slimmpylk/Sport-smartwatch-project/docs/project/post_footprint_freeze_sanity.md

# Post-Footprint Freeze Sanity Review & Final Resolution Report

Date: 2026-10-06  
Project: `sportwatch_revA` (Premium Outdoor/Endurance Smartwatch PCBA)  
Baseline Commit: `1b691c32fff54d33248b8b00c434d59538cc4d53`  
Native Engine: KiCad CLI 10.0.5 via Flatpak runtime  
Electrical Baseline: 0 ERC errors, checked=83 mismatches=0, 389 electrical nets  

---

## 1. Executive Decision

```text
============================================================
FOOTPRINT FREEZE: PASS
============================================================
```

All three post-footprint freeze sanity review mandates have been rigorously investigated, resolved, and verified against primary manufacturer documentation and native KiCad validation gates:
1. **384 `lib_symbol_issues` Warning Root Cause Resolved:** Root cause was traced to a Flatpak container environment path discrepancy (`KICAD10_SYMBOL_DIR` pointing to an unmounted host directory). Resolved at the CLI environment level without suppressing warnings or altering schematic symbol semantics. Native `lib_symbol_issues` count is now **exactly 0**.
2. **Crystals Y1 & Y102 Re-Audited & Grounded:** Primary manufacturer datasheets (NDK NX1612SA and Nordic/Ambiq specifications) confirm physical pads 2 and 4 are case-ground terminals internally bonded to the metal cover lid. Grounding is mandatory for RF harmonic shielding and clock jitter immunity. A project-local 4-pad footprint `sportwatch_custom:Crystal_1612-4Pin_1.6x1.2mm` and 4-pin grounded symbol `sportwatch_custom:Crystal_1612-4Pin_GND` were created and integrated. Active oscillator nets (`Net-(U9-XOP)`, `Net-(U9-XON)`, `APOLLO_BLE_XIN`, `APOLLO_BLE_XOUT`) remain 100% preserved, while pads 2 and 4 are connected to `GND`.
3. **Mechanically Dependent Parts Reclassified to Class C:** Buttons SW1..SW5, battery interface J201, and charging pogo interface J202 were verified to lack frozen mechanical 3D enclosure CAD or tooling evidence. In strict adherence to project policy ("Missing/TBD is strictly preferred over guessing unverified footprints"), all seven components are reclassified as **Class C (valid electrical candidate, mechanically TBD)** and their footprint fields set to blank (`""`).
4. **Final Gate Verification:** Native KiCad ERC reports **0 errors**; hierarchical interfaces report **`checked=83 mismatches=0`**; netlist comparison confirms zero unintended net changes; footprint resolution check confirms 100% of 228 assigned footprints resolve cleanly; and `sportwatch_revA.kicad_pcb` remains completely **untouched**.

---

## 2. Investigation of 384 `lib_symbol_issues`

### 2.1 Problem Statement
Native KiCad ERC initially reported 384 instances of `lib_symbol_issues`. KiCad ERC flags this warning when a referenced symbol library cannot be located by the schematic parser or when a referenced symbol cannot be resolved within the library table.

### 2.2 Forensic Analysis & Root Cause Identification
A automated breakdown of all 384 warnings from `kicad-cli sch erc --format json` revealed:
| Library Nickname | Affected Component Class | Warning Count | Example Missing Path Reported by KiCad |
|---|---|---:|---|
| `power` | Global power ports (`GND`, `+1V8`, `+3V3`, `VBAT`, etc.) | 203 | `/var/lib/flatpak/runtime/org.kicad.KiCad.Library.Symbols/.../power.kicad_sym` |
| `Device` | Standard R, C, L passives, ferrite beads, test pads | 173 | `/var/lib/flatpak/runtime/org.kicad.KiCad.Library.Symbols/.../Device.kicad_sym` |
| `Switch` | Tactile switches | 5 | `/var/lib/flatpak/runtime/org.kicad.KiCad.Library.Symbols/.../Switch.kicad_sym` |
| `Connector_Generic` | Generic headers / interfaces | 2 | `/var/lib/flatpak/runtime/org.kicad.KiCad.Library.Symbols/.../Connector_Generic.kicad_sym` |
| `Regulator_Switching` | Switching regulator generic | 1 | `/var/lib/flatpak/runtime/org.kicad.KiCad.Library.Symbols/.../Regulator_Switching.kicad_sym` |
| **Total** | | **384** | |

**Exact Technical Cause:**
- KiCad 10 is executed in this environment via Flatpak (`org.kicad.KiCad`).
- The Flatpak build manifest sets the runtime environment variable `KICAD10_SYMBOL_DIR` to the host installation path (`/var/lib/flatpak/runtime/org.kicad.KiCad.Library.Symbols/x86_64/stable/.../files/symbols`).
- However, inside Flatpak's isolated mount namespace (container sandbox), `/var/lib/flatpak` does **not exist**. The Flatpak runtime extension actually mounts the symbol library at `/app/extensions/Library/symbols/`.
- Because the environment variable `KICAD10_SYMBOL_DIR` takes precedence over `kicad_common.json` configuration, KiCad CLI attempted to search the non-existent `/var/lib/flatpak/...` path when expanding `${KICAD10_SYMBOL_DIR}` in the standard symbol library table `/app/extensions/Library/template/sym-lib-table`.
- Consequently, all 384 standard KiCad components fell back to their cached schematic definitions while issuing `lib_symbol_issues` warnings.

### 2.3 Permanent Resolution
The issue was resolved cleanly at the CLI execution layer without altering schematic symbol definitions or hiding ERC warnings:
1. Updated the wrapper script `/home/sapy/.local/bin/kicad-cli` to pass `--env=KICAD10_SYMBOL_DIR=/app/extensions/Library/symbols` into `flatpak run`.
2. Verified that KiCad CLI `-D KICAD10_SYMBOL_DIR=/app/extensions/Library/symbols` also natively overrides this path.
3. Reran native ERC on the entire project:
   - **`lib_symbol_issues` warnings: 0** (100% resolved).
   - ERC errors: **0**.
   - Total warnings dropped from 1551 to the baseline gate level (1172 warnings, consisting of existing off-grid cosmetic coordinates and intentional isolated test points).

---

## 3. Re-Audit of Crystals Y1 and Y102

### 3.1 Components & Primary Datasheet Sources
- **Y1 (Wi-Fi 40 MHz Reference Clock):**
  - Application: Nordic nRF7002 Wi-Fi 6 companion IC high-frequency crystal oscillator.
  - Primary Datasheet: Nordic Semiconductor nRF7002 Product Specification (v1.2, §14.3 BOM table, §5.3 Clock accuracy).
  - Manufacturer & MPN: **NDK (Nihon Dempa Kogyo) NX1612SA-40M-EXS00A-CS14264** (Alternate: Murata `XRCGB40M000F4M00R0` / Epson `FA-128`).
  - Electrical Spec: 40.000 MHz, CL = 8 pF, ESR <= 100 Ω, tolerance/stability <= +/-10 ppm (satisfying IEEE 802.11 +/-20 ppm budget).
- **Y102 (MCU 48 MHz Reference Clock):**
  - Application: Ambiq Apollo510B MCU high-speed crystal oscillator (BLE radio and system PLL reference).
  - Primary Datasheet: Ambiq Apollo510B SoC Datasheet (DS-A510B-1p1p0, Table 50: High-Speed Crystal Oscillator, Page 230).
  - Manufacturer & MPN: **NDK NX1612SA-48M-EXS00A-CS14265** (Alternate: Murata `XRCGB48M000F4M00R0`).
  - Electrical Spec: 48.000 MHz, CL = 8 to 11 pF, ESR <= 60 Ω, frequency deviation <= +/-50 ppm.

### 3.2 Physical Package Drawing & Pad Function
Per NDK NX1612SA mechanical drawing (1.6 mm x 1.2 mm x 0.4 mm max):
- **Pad 1 (Bottom-Left, marked with index notch):** Crystal Terminal 1 (active piezoelectric electrode).
- **Pad 2 (Bottom-Right):** Case Ground / Cover Shield (internally seam-welded to the Kovar protective lid).
- **Pad 3 (Top-Right):** Crystal Terminal 2 (active piezoelectric electrode).
- **Pad 4 (Top-Left):** Case Ground / Cover Shield (internally seam-welded to the Kovar protective lid).

### 3.3 Functional Classification of Pads 2 and 4
Pads 2 and 4 are classified as **MANDATORY GND** for this wearable PCBA:
1. **RF Harmonic Shielding:** In high-frequency oscillators (40 MHz and 48 MHz), an ungrounded metal lid acts as an efficient patch radiator. The 40 MHz harmonics fall directly into the GNSS L1 band (39th harmonic @ 1560 MHz), cellular LTE/5G bands, and the 2.4 GHz ISM band (60th harmonic). Grounding pads 2 and 4 forms a complete Faraday cage around the quartz element.
2. **Noise Immunity:** Floating the lid allows fast digital edges (e.g. Apollo510B QSPI at 48 MHz or PMIC buck switching nodes) to couple capacitively into the high-impedance crystal input (`XOP` / `APOLLO_BLE_XIN`), causing clock jitter and phase noise.
3. **Frequency Pulling Prevention:** Body capacitance (watch user skin proximity) or proximity to a metallic watch bezel will modulate the parasitic capacitance of a floating lid, causing carrier frequency drift.

Leaving physical pads 2 and 4 as isolated unnumbered solder pads was therefore an electrical risk.

### 3.4 Symbol & Footprint Implementation
1. **Footprint Creation (`Crystal_1612-4Pin_1.6x1.2mm`):**
   Created `sportwatch_custom:Crystal_1612-4Pin_1.6x1.2mm` in `sportwatch_custom.pretty`.
   - Pad 1: smd roundrect `(-0.525, 0.4)`, size `0.75 x 0.6 mm` (X1 active)
   - Pad 2: smd roundrect `(0.525, 0.4)`, size `0.75 x 0.6 mm` (GND shield)
   - Pad 3: smd roundrect `(0.525, -0.4)`, size `0.75 x 0.6 mm` (X2 active)
   - Pad 4: smd roundrect `(-0.525, -0.4)`, size `0.75 x 0.6 mm` (GND shield)
   - Dimensions verified against IPC-7351B and NDK recommended land pattern.
2. **Symbol Definition (`Crystal_1612-4Pin_GND`):**
   Created symbol `sportwatch_custom:Crystal_1612-4Pin_GND` in `libraries/symbols/sportwatch_custom.kicad_sym` and cached in child sheets `01_APOLLO510B` and `06_WIFI`:
   - Pin 1 (X1): at `(-7.62, 0)`, passive line length 5.08 mm. Mates seamlessly with existing schematic wires at `(168.38, 150)` in sheet 06 and `(382.38, 104)` in sheet 01.
   - Pin 3 (X2): at `(7.62, 0)`, passive line length 5.08 mm. Mates seamlessly with existing schematic wires at `(183.62, 150)` in sheet 06 and `(397.62, 104)` in sheet 01.
   - Pin 2 (GND) & Pin 4 (GND): stacked at `(0, 5.08, 270)`, passive line length 1.27 mm.
   - Tied to `GND` via native `power:GND` symbols at `(176, 144.92)` in sheet 06 and `(390, 98.92)` in sheet 01.
3. **Signal Preservation Verification:**
   - Wi-Fi nets `Net-(U9-XOP)` (pin 1) and `Net-(U9-XON)` (pin 3) remain 100% intact.
   - Apollo MCU nets `/01_APOLLO510B/APOLLO_BLE_XIN` (pin 1) and `/01_APOLLO510B/APOLLO_BLE_XOUT` (pin 3) remain 100% intact.
   - Only the global `GND` net received the four case-shield connections (`Y1.2`, `Y1.4`, `Y102.2`, `Y102.4`).

---

## 4. Reclassification of Mechanically Dependent Parts

### 4.1 Audit Scope
Review of mechanical boundary parts assigned in commit `1b691c3`:
- Push Buttons: `SW1..SW5`
- Battery Interface: `J201`
- Charging Interface: `J202`

### 4.2 Engineering Verification against Mechanical Enclosure Context

| Reference | Function | Candidate Part in Commit 1b691c3 | Mechanical Verification Findings | Classification Decision |
|---|---|---|---|:---:|
| **SW1..SW5** | 5x Tactile Push Buttons (Light, Up, Down, Start, Back) | Panasonic `EVQP7A04M` side-push switch (`Button_Switch_SMD:SW_SPST_EVQP7A`) | In a 49–52 mm rugged sports watch with 5 ATM / 50m water resistance, button plungers require silicone O-ring sealing within the casing wall. Pusher pin height, travel (0.2 mm vs 0.4 mm), stroke force, and PCB edge setback (+/-0.1 mm tolerance) are undefined by 3D CAD. Circular sports watches frequently route buttons on a perimeter flexible PCB (FPC) rather than rigid PCB edges to prevent board warping under 2.2 N actuation forces. Freezing EVQP7A without case CAD is unverified. | **Class C** (Valid electrical candidate, Mechanically TBD) |
| **J201** | LiPo Pouch Cell Battery Interface | `sportwatch_custom:BatteryPad_3Pin_SMD` (1.8 mm pitch SMD pads) | Pouch cell termination architecture depends entirely on battery supplier tooling: (a) pre-soldered flying wire leads (Red/White/Black), (b) board-to-FPC micro connector (Hirose BM28 / Molex 503772), or (c) spring-loaded carrier contacts. Footprint was an unverified placeholder. | **Class C** (Valid electrical candidate, Mechanically TBD) |
| **J202** | External Charging / Pogo Interface | `sportwatch_custom:PogoPad_2Pin_SMD` (2.5 mm pitch, D1.5 mm pads) | External charging contacts depend on magnetic cable puck tooling: center spacing (2.5 mm vs 2.84 mm vs custom puck), case rear recess, gasket sealing, and gold plating metallurgy (hard gold / ENEPIG / Au 30 µinch min to resist sweat galvanic corrosion). Footprint was an unverified placeholder. | **Class C** (Valid electrical candidate, Mechanically TBD) |

### 4.3 Action Taken
In strict compliance with the footprint audit gate rules ("Do NOT freeze a component merely because its footprint is manufacturable. If mechanical information is not yet defined, reclassify as Class C"):
- In `11_BUTTONS.kicad_sch`: Cleared footprint fields of `SW1`, `SW2`, `SW3`, `SW4`, and `SW5` to empty string (`""`).
- In `02_POWER.kicad_sch`: Cleared footprint fields of `J201` and `J202` to empty string (`""`).
- Total Class C deferred inventory updated to **exactly 15 components**.

---

## 5. Comprehensive PCBA Component Classification Audit

With the reclassifications applied, all 243 physical components are accounted for across the physical PCBA:

| Classification | Count | Percentage | Definition & Scope |
|---|---:|---:|---|
| **Class A** | 45 | 18.5% | Exact MPN & primary manufacturer package drawings fully verified (ICs, optical BioFY/PD/IR devices, sensors, power converters, 4-pad crystals Y1 & Y102, display connector J1, debug connector J1301) |
| **Class B** | 183 | 75.3% | Standard passives assigned per project policy (0402/0603/0201 passives, switching inductors, net ties, test points) |
| **Class C** | 15 | 6.2% | Valid electrical candidates intentionally deferred pending mechanical CAD, pouch cell procurement, dock tooling, or RF chamber tuning |
| **Class D** | 0 | 0.0% | Unexpectedly missing footprints |
| **Class E** | 0 | 0.0% | Incorrect or unsafe footprints |
| **Total** | **243** | **100.0%** | **Complete Physical PCBA BOM** |

### Complete 15-Item Class C Inventory:
1. `AE1401` — Bluetooth LE Antenna (watch bezel slot vs LDS antenna)
2. `AE1410` — Wi-Fi 2.4/5GHz Dual-Band Antenna (case material & aperture)
3. `AE1420` — GNSS L1/L5 Dual-Band Antenna (metal bezel slot & polarization)
4. `TP1401` — BLE RF Conducted Test Port (micro-coax switch vs GSG pad array)
5. `TP1410` — Wi-Fi RF Conducted Test Port (micro-coax switch vs GSG pad array)
6. `TP1420` — GNSS RF Conducted Test Port (micro-coax switch vs GSG pad array)
7. `U10` — Wi-Fi 2.4/5GHz Diplexer (0605 vs 0805 layout density)
8. `LRA1` — Haptic Linear Resonant Actuator (coin vs bar motor internal pocket)
9. `SW1` — Button Light (Panasonic EVQP7A side push vs perimeter flex FPC)
10. `SW2` — Button Up (Panasonic EVQP7A side push vs perimeter flex FPC)
11. `SW3` — Button Down (Panasonic EVQP7A side push vs perimeter flex FPC)
12. `SW4` — Button Start (Panasonic EVQP7A side push vs perimeter flex FPC)
13. `SW5` — Button Back (Panasonic EVQP7A side push vs perimeter flex FPC)
14. `J201` — Battery Interface (soldered leads vs Hirose BM28 micro-connector vs spring contact)
15. `J202` — Charging Interface (magnetic puck 2.5mm vs 2.84mm vs hard-gold skin pads)

---

## 6. Final Gate Validation Results

The complete project was validated using native KiCad CLI 10.0.5:

| Verification Gate | Requirement | Measured Result | Status |
|---|---|---|---|
| **Native KiCad ERC Errors** | Exactly 0 errors | **0 errors** | **PASS** |
| **`lib_symbol_issues`** | Exactly 0 warnings | **0 warnings** | **PASS** |
| **Total ERC Warnings** | Baseline gate parity (<= 1172) | **1172 warnings** (1154 off-grid cosmetic, 7 isolated label, 5 pin-to-pin, 3 cached mismatch, 2 multi-wire, 1 wire stub) | **PASS** |
| **Hierarchical Interfaces** | checked=83 mismatches=0 | **checked=83 mismatches=0** | **PASS** |
| **Native Netlist Generation** | Zero unannotated errors | Exits 0, 243 components, 389 nets | **PASS** |
| **Unintended Net Changes** | Zero unintended net alterations | **0 unintended changes** across all 389 nets (only intentional Y1/Y102 signal pin-3 remapping and GND lid additions) | **PASS** |
| **Footprint Resolution** | 100% of assigned footprints resolve | **228 / 228 resolve cleanly** (0 custom missing, 0 standard missing) | **PASS** |
| **Blank Footprint Count** | Exactly 15 Class C components | **Exactly 15 blank footprints** | **PASS** |
| **PCB Layout State** | `sportwatch_revA.kicad_pcb` untouched | **File completely untouched** (0 bytes modified) | **PASS** |

---

## 7. Gate Conclusion & Next Steps

The post-footprint freeze sanity review is **100% COMPLETE AND PASSED**.

- The schematic remains electrically frozen and verified.
- Symbol library resolution is robust and error-free.
- High-frequency crystals Y1 and Y102 are properly grounded for RF performance and signal integrity.
- Mechanical boundary parts are properly segregated into Class C pending mechanical engineering release.
- The design is in a state ready to proceed to preliminary PCB board outline and mechanical keepout definition when authorized by the user.
