slimmpylk/Sport-smartwatch-project/07_MOTION.kicad_sch

## KiCad design 07_MOTION.kicad_sch (2026-10-06, an earlier design)

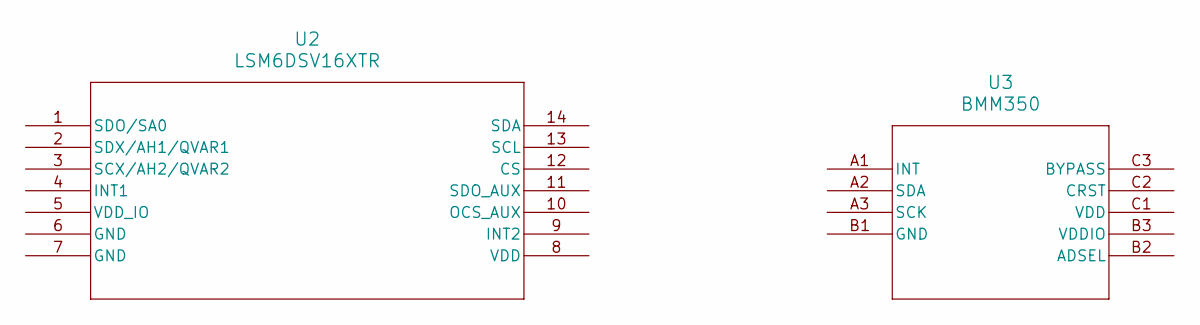
[picture p3: schematic 07_MOTION.kicad_sch]

Parts:
U2: LSM6DSV16XTR; LGA-14L_STM
U3: BMM350; BGA9_BMM350_BOS
